ryan-ma/PD_Micro/PD_Micro/src/PD_UFP.h

/**
 * PD_UFP.h
 *
 *  Updated on: Jan 25, 2021
 *      Author: Ryan Ma
 *
 * Minimalist USB PD Ardunio Library for PD Micro board
 * Only support UFP(device) sink only functionality
 * Requires FUSB302_UFP.h, PD_UFP_Protocol.h and Standard Arduino Library
 *
 * Support PD3.0 PPS
 * 
 */

#ifndef PD_UFP_H
#define PD_UFP_H

#include <stdint.h>

#include <Arduino.h>
#include <Wire.h>
#include <HardwareSerial.h>

extern "C" {
    #include "FUSB302_UFP.h"
    #include "PD_UFP_Protocol.h"
}

enum {
    PD_UFP_VOLTAGE_LED_OFF      = 0,
    PD_UFP_VOLTAGE_LED_5V       = 1,
    PD_UFP_VOLTAGE_LED_9V       = 2,
    PD_UFP_VOLTAGE_LED_12V      = 3,
    PD_UFP_VOLTAGE_LED_15V      = 4,
    PD_UFP_VOLTAGE_LED_20V      = 5,
    PD_UFP_VOLTAGE_LED_AUTO     = 6
};
typedef uint8_t PD_UFP_VOLTAGE_LED_t;

enum {
    PD_UFP_CURRENT_LED_OFF      = 0,
    PD_UFP_CURRENT_LED_LE_1V    = 1,
    PD_UFP_CURRENT_LED_LE_3V    = 2,
    PD_UFP_CURRENT_LED_GT_3V    = 3,
    PD_UFP_CURRENT_LED_AUTO     = 4    
};
typedef uint8_t PD_UFP_CURRENT_LED_t;

enum {
    STATUS_POWER_NA = 0,
    STATUS_POWER_TYP,
    STATUS_POWER_PPS
};
typedef uint8_t status_power_t;

///////////////////////////////////////////////////////////////////////////////////////////////////
// PD_UFP_core_c
///////////////////////////////////////////////////////////////////////////////////////////////////
class PD_UFP_core_c
{
    public:
        PD_UFP_core_c();
        // Init
        void init(enum PD_power_option_t power_option = PD_POWER_OPTION_MAX_5V);
        void init_PPS(uint16_t PPS_voltage, uint8_t PPS_current, enum PD_power_option_t power_option = PD_POWER_OPTION_MAX_5V);
        // Task
        void run(void);
        // Status
        bool is_power_ready(void) { return status_power == STATUS_POWER_TYP; }
        bool is_PPS_ready(void)   { return status_power == STATUS_POWER_PPS; }
        bool is_ps_transition(void) { return send_request || wait_ps_rdy; }
        // Get
        uint16_t get_voltage(void) { return ready_voltage; }    // Voltage in 50mV units, 20mV(PPS)
        uint16_t get_current(void) { return ready_current; }    // Current in 10mA units, 50mA(PPS)
        // Set
        bool set_PPS(uint16_t PPS_voltage, uint8_t PPS_current);
        void set_power_option(enum PD_power_option_t power_option);
        // Clock
        static void clock_prescale_set(uint8_t prescaler);

    protected:
        static FUSB302_ret_t FUSB302_i2c_read(uint8_t dev_addr, uint8_t reg_addr, uint8_t *data, uint8_t count);
        static FUSB302_ret_t FUSB302_i2c_write(uint8_t dev_addr, uint8_t reg_addr, uint8_t *data, uint8_t count);
        static FUSB302_ret_t FUSB302_delay_ms(uint32_t t);
        void handle_protocol_event(PD_protocol_event_t events);
        void handle_FUSB302_event(FUSB302_event_t events);
        bool timer(void);
        void set_default_power(void);
        // Device
        FUSB302_dev_t FUSB302;
        PD_protocol_t protocol;
        // Power ready power
        uint16_t ready_voltage;
        uint16_t ready_current;
        // PPS setup
        uint16_t PPS_voltage_next;
        uint8_t PPS_current_next;
        // Status
        virtual void status_power_ready(status_power_t status, uint16_t voltage, uint16_t current);
        uint8_t status_initialized;
        uint8_t status_src_cap_received;
        status_power_t status_power;
        // Timer and counter for PD Policy
        uint16_t time_polling;
        uint16_t time_wait_src_cap;
        uint16_t time_wait_ps_rdy;
        uint16_t time_PPS_request;
        uint8_t get_src_cap_retry_count;
        uint8_t wait_src_cap;
        uint8_t wait_ps_rdy;
        uint8_t send_request;
        static uint8_t clock_prescaler;
        // Time functions        
        void delay_ms(uint16_t ms);
        uint16_t clock_ms(void);
        // Status logging
        virtual void status_log_event(uint8_t status, uint32_t * obj = 0) {}
};

///////////////////////////////////////////////////////////////////////////////////////////////////
// PD_UFP_c, extended from PD_UFP_core_c, Add LED and Load switch functions
///////////////////////////////////////////////////////////////////////////////////////////////////
class PD_UFP_c : public PD_UFP_core_c
{
    public:
        PD_UFP_c();
        // Set LED
        void set_led(uint8_t enable);
        void set_led(PD_UFP_VOLTAGE_LED_t index_v, PD_UFP_CURRENT_LED_t index_a);
        void blink_led(uint16_t period);
        // Set Load Switch
        void set_output(uint8_t enable);
        // Task
        void run(void);

    protected:
        // Status
        virtual void status_power_ready(status_power_t status, uint16_t voltage, uint16_t current);
        // LED
        uint8_t led_blink_enable;
        uint8_t led_blink_status;
        uint16_t time_led_blink;
        uint16_t period_led_blink;
        PD_UFP_VOLTAGE_LED_t led_voltage;
        PD_UFP_CURRENT_LED_t led_current;
        void calculate_led(uint16_t voltage, uint16_t current);
        void calculate_led_pps(uint16_t PPS_voltage, uint8_t PPS_current);
        void update_voltage_led(PD_UFP_VOLTAGE_LED_t index);
        void update_current_led(PD_UFP_CURRENT_LED_t index);
        void handle_led(void);
        // Load Switch
        uint8_t status_load_sw;
};



///////////////////////////////////////////////////////////////////////////////////////////////////
// Optional: PD_UFP_log_c, extended from PD_UFP_c to provide logging function.
//           Asynchronous, minimal impact on PD timing.
///////////////////////////////////////////////////////////////////////////////////////////////////
struct status_log_t {
    uint16_t time;
    uint16_t msg_header;
    uint8_t obj_count;
    uint8_t status;
};

enum pd_log_level_t {
    PD_LOG_LEVEL_INFO,
    PD_LOG_LEVEL_VERBOSE
};

class PD_UFP_log_c : public PD_UFP_c
{
    public:
        PD_UFP_log_c(pd_log_level_t log_level = PD_LOG_LEVEL_INFO);
        // Task
        void print_status(Serial_ & serial);
        void print_status(HardwareSerial & serial);
        // Get
        int status_log_readline(char * buffer, int maxlen);

    protected:
        int status_log_readline_msg(char * buffer, int maxlen, status_log_t * log);
        int status_log_readline_src_cap(char * buffer, int maxlen);
        // Status log functions
        uint8_t status_log_obj_add(uint16_t header, uint32_t * obj);
        virtual void status_log_event(uint8_t status, uint32_t * obj);
        // status log event queue
        status_log_t status_log[16];    // array size must be power of 2 and <=256
        uint8_t status_log_read;
        uint8_t status_log_write;
        // status log object queue
        uint32_t status_log_obj[16];    // array size must be power of 2 and <=256
        uint8_t status_log_obj_read;
        uint8_t status_log_obj_write;
        // state variables
        pd_log_level_t status_log_level;
        uint8_t status_log_counter;        
        char status_log_time[8];
};

#endif
